monsonite/TICK/Program_Counter.jpg

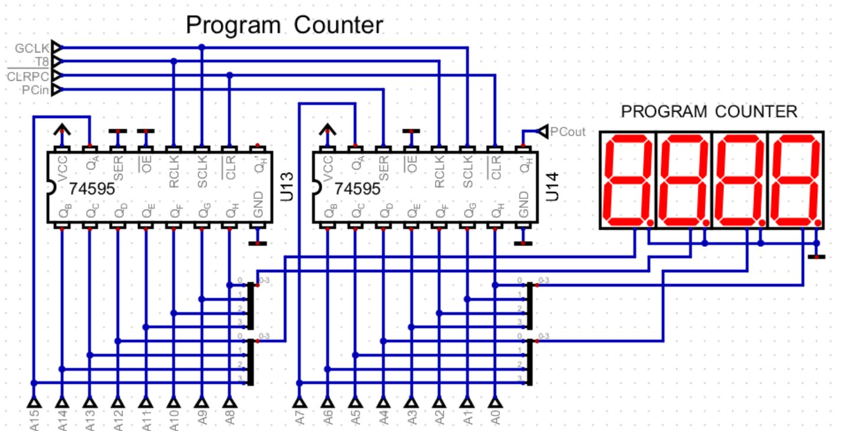
Program_Counter.jpg
