monsonite/TICK/SRAM_NANO.jpg

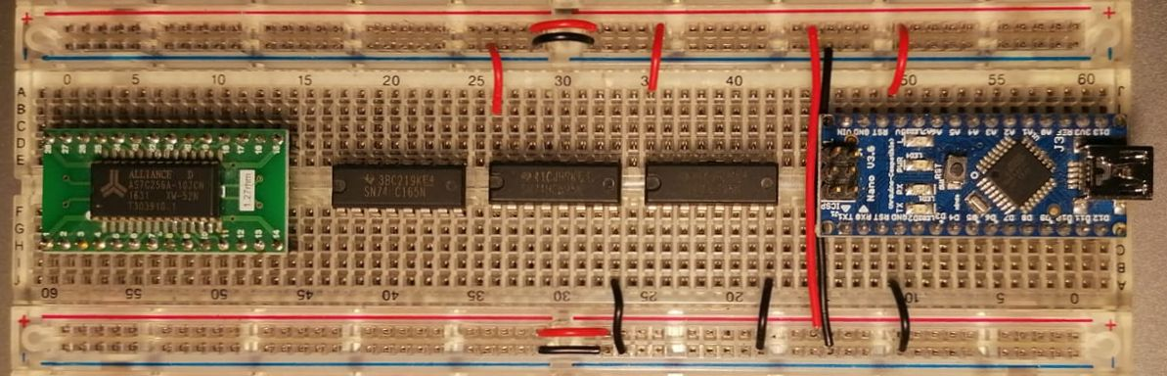
SRAM_NANO.jpg
