monsonite/TICK/Testboard_13.jpg

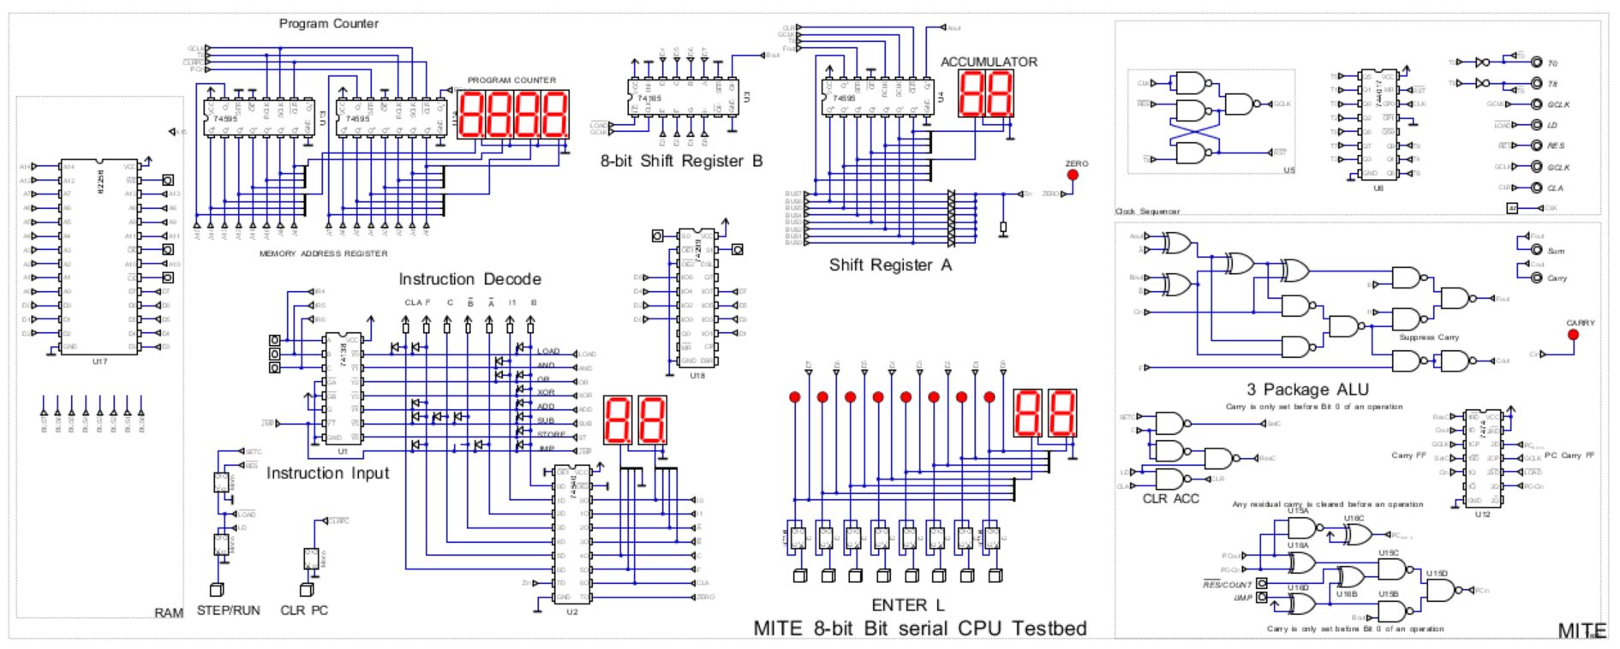
Testboard_13.jpg
